bmarkslash7/logTHIS/pcb/gcode/dht22_sensor_schem/outp0_original_back.png

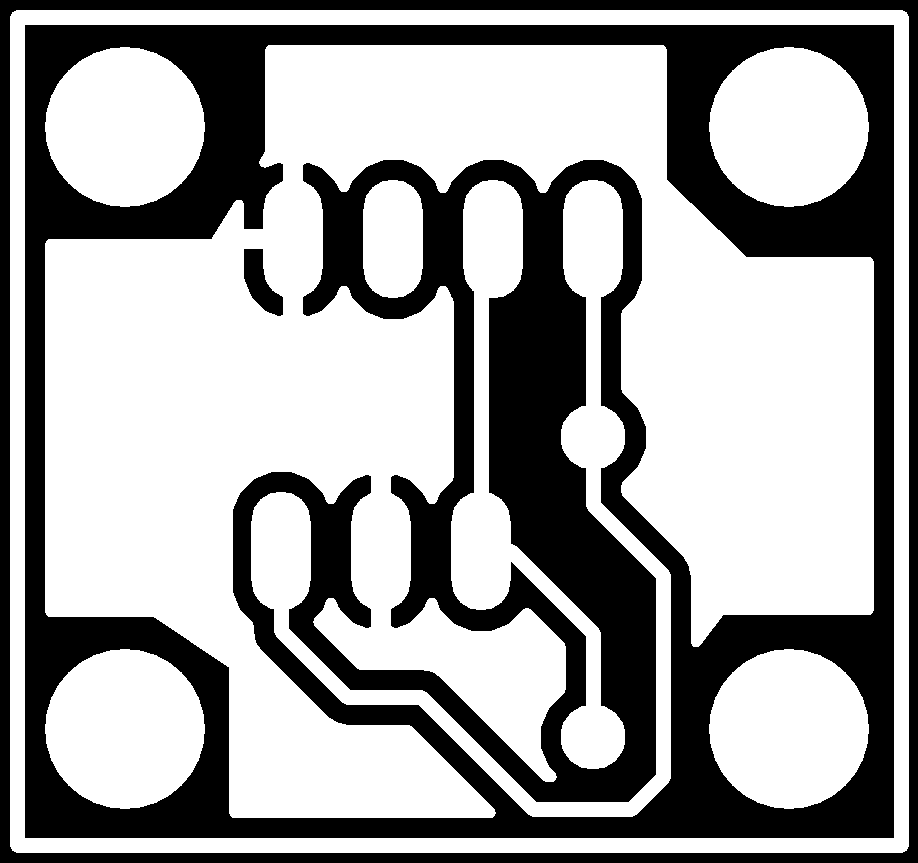
pcb/gcode/dht22_sensor_schem/outp0_original_back.png
