bmarkslash7/logTHIS/pcb/gcode/dht22_sensor_schem/outp1_original_front.png

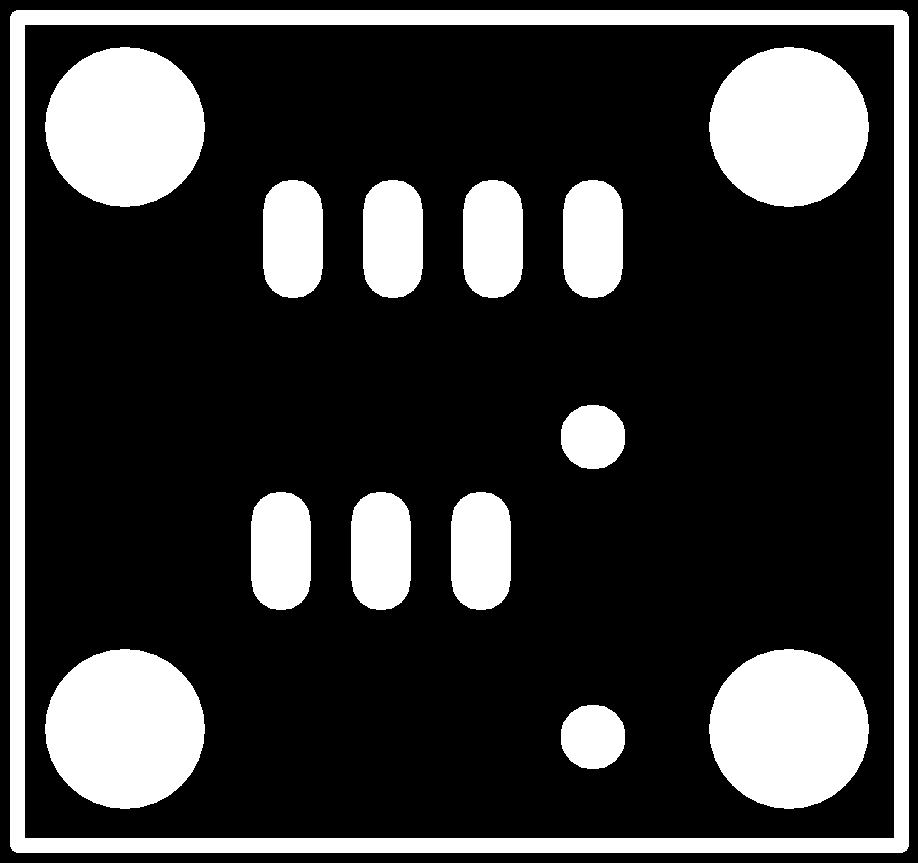
pcb/gcode/dht22_sensor_schem/outp1_original_front.png
