bmarkslash7/logTHIS/pcb/gcode/dht22_sensor_schem/outp3_traced.png

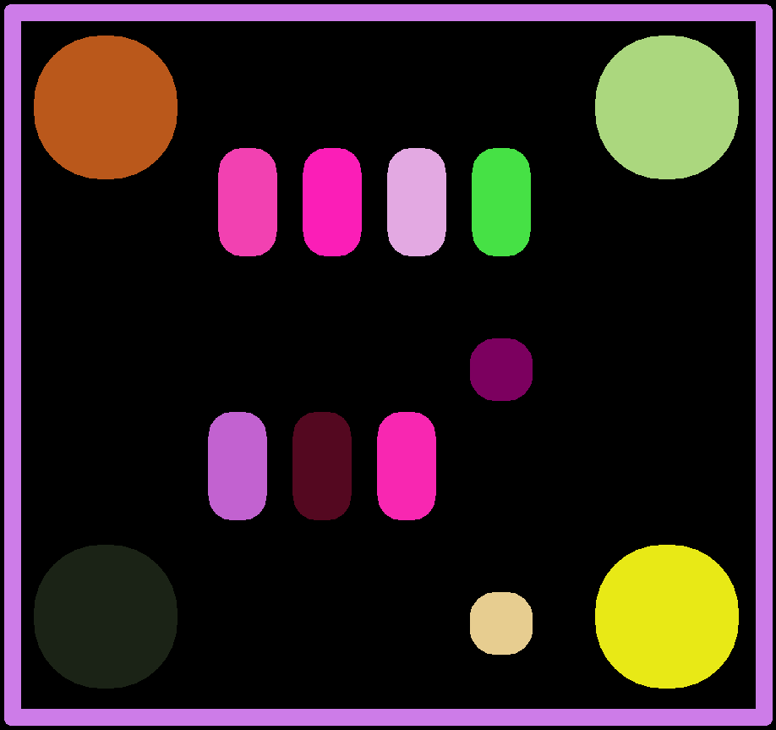
pcb/gcode/dht22_sensor_schem/outp3_traced.png
