bmarkslash7/logTHIS/pcb/gcode/logTHIS/outp0_original_back.png

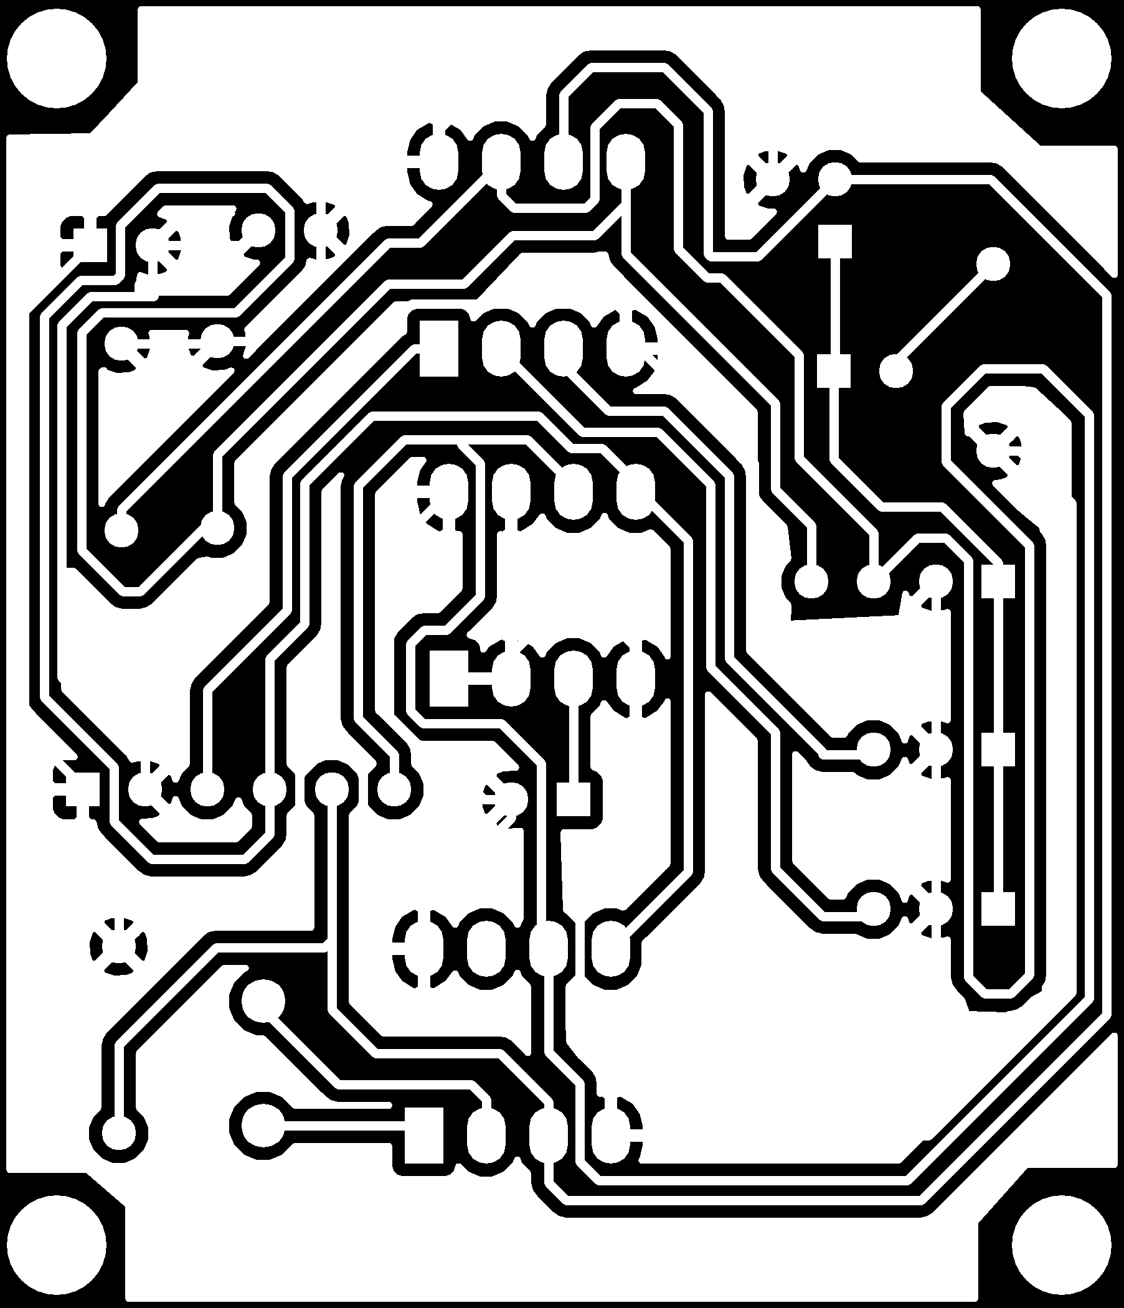
pcb/gcode/logTHIS/outp0_original_back.png
