bmarkslash7/logTHIS/pcb/gcode/logTHIS/outp2_traced.png

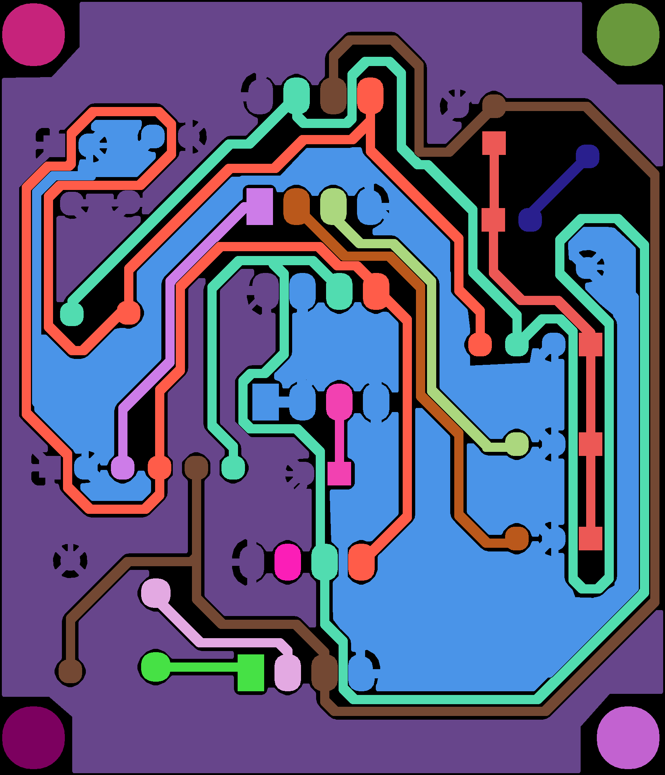
pcb/gcode/logTHIS/outp2_traced.png
