bmarkslash7/logTHIS/pcb/gcode/logTHIS/outp3_traced.png

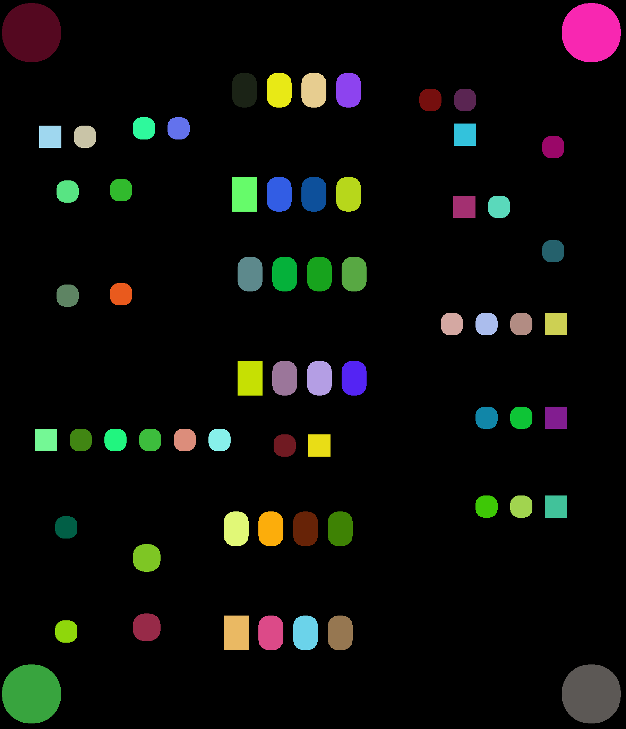
pcb/gcode/logTHIS/outp3_traced.png
