bmarkslash7/logTHIS/pcb/dht22_sensor_schem/dht22_sensor_schem.sch

## KiCad design pcb/dht22_sensor_schem/dht22_sensor_schem.sch (2013-02-22)

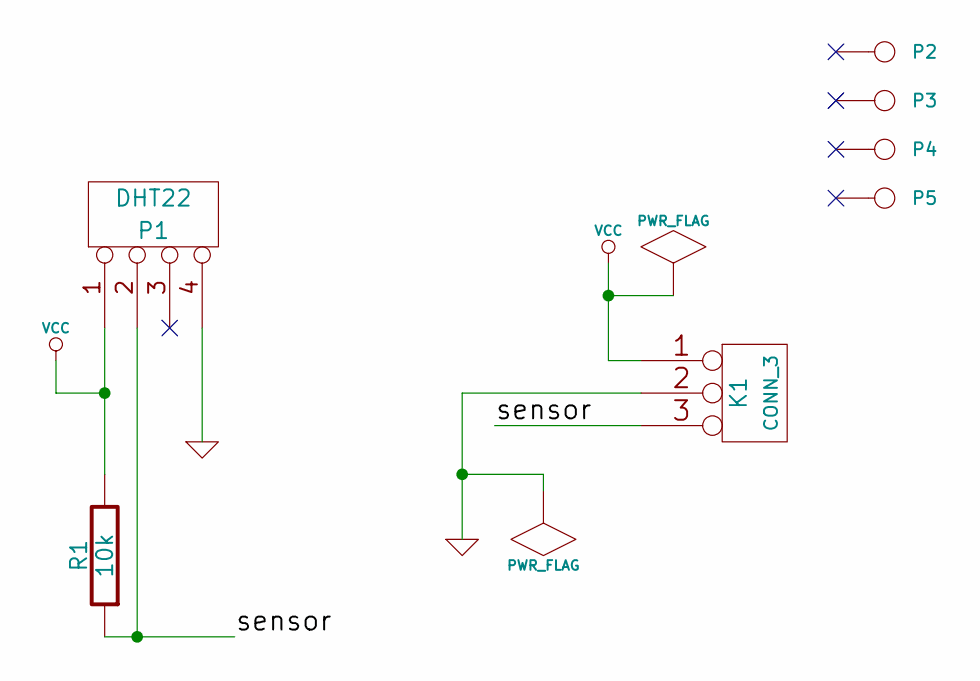
[picture p13: schematic dht22_sensor_schem.sch]

Parts:
K1: CONN_3
P1: DHT22
P2, P3, P4, P5: CONN_1
R1: 10k

Connections:
GND: K1.2 (PM), P1.4
VCC: K1.1, P1.1, R1.2
sensor: K1.3, P1.2, R1.1
