bmarkslash7/logTHIS/schematic/schem/logTHIS.sch

## KiCad design schematic/schem/logTHIS.sch (2013-02-06, an earlier design)

Schematic: logTHIS.sch

Parts:
C1: .1mF
D1: LED
K1: Sensor1
K2: Sensor0
P1: CONN_6
P2: Battery
P3: I2C Sense
P4: PWR_JMP
Q1: MOSFET_N
R1: 10k
R2, R3: 4.7k
R4: 1k
U1: 24AA1025; MODULE
U2: DS1337; MODULE
U3: ATTINY85V; MODULE
X1: 32.768 kHz
